SynthexBTC/Bitcoin-LoRa-Mesh/Solar-nRF52840-E22P868M30S/PCB/README.md

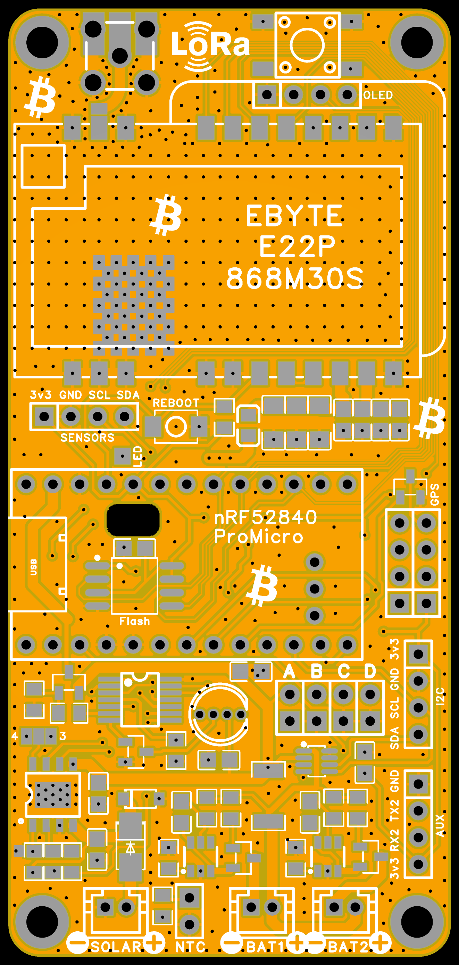
[picture p74: Solar-nRF52840-E22P868M30S/images/BitcoinMesh Solar nRF52840 E22P-868M30S - PCB Top.png]
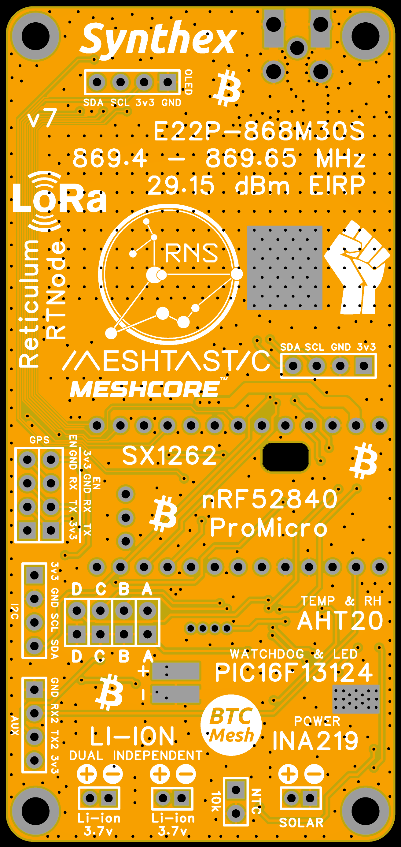
[picture p75: Solar-nRF52840-E22P868M30S/images/BitcoinMesh Solar nRF52840 E22P-868M30S - PCB Bottom.png]
&nbsp;&nbsp;
