SynthexBTC/Bitcoin-LoRa-Mesh/Module-nRF52840-E22P868M30S/PCB/README.md

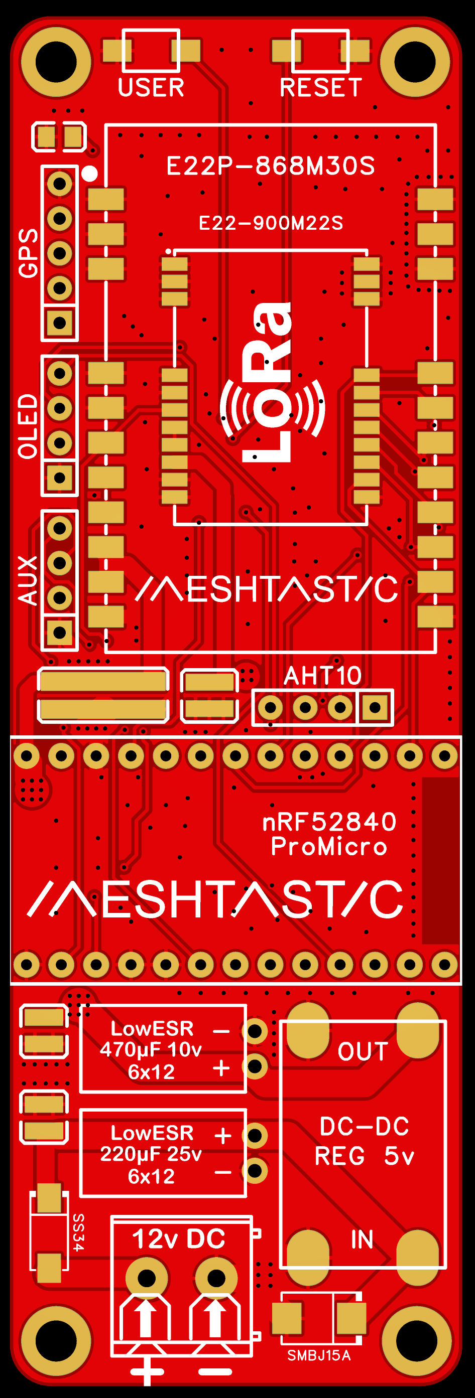
[picture p76: Module-nRF52840-E22P868M30S/images/BitcoinMesh HighPower Module nRF52840 - PCB Top.png]
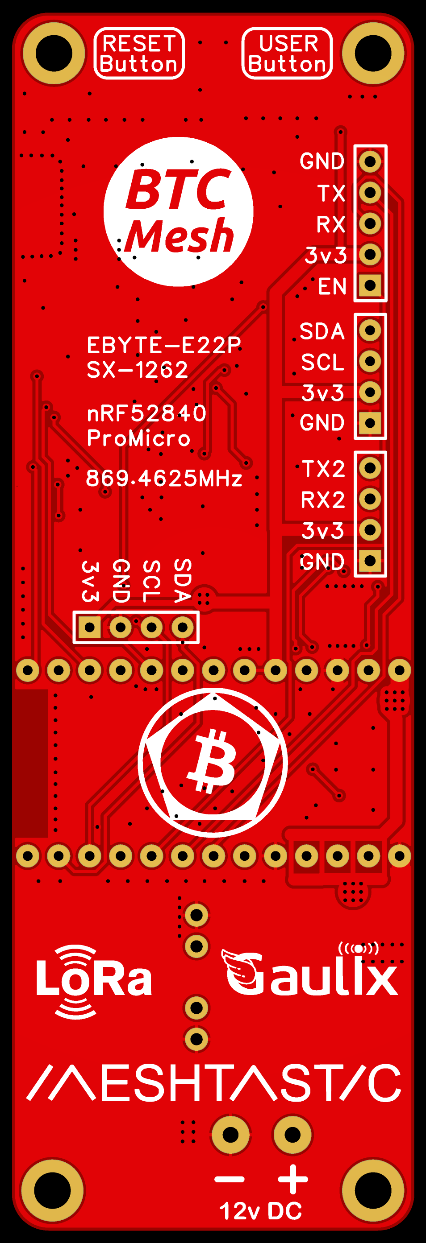
[picture p77: Module-nRF52840-E22P868M30S/images/BitcoinMesh HighPower Module nRF52840 - PCB Bottom.png]
&nbsp;&nbsp;
