SynthexBTC/Bitcoin-LoRa-Mesh/Module-nRF52840-HTRA62/PCB/README.md

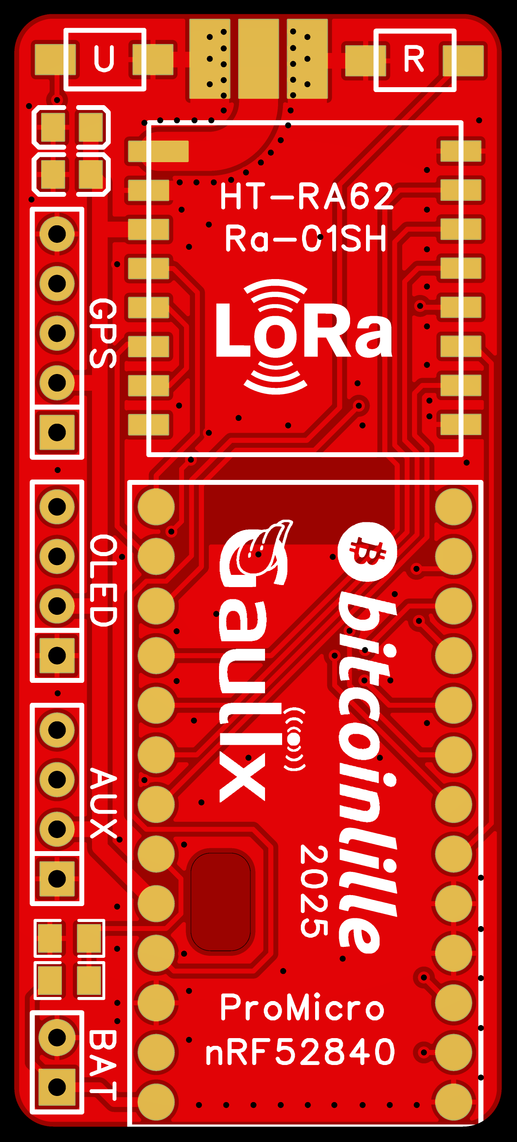
[picture p78: Module-nRF52840-HTRA62/images/BitcoinMesh Module nRF52840 - PCB Top.png]
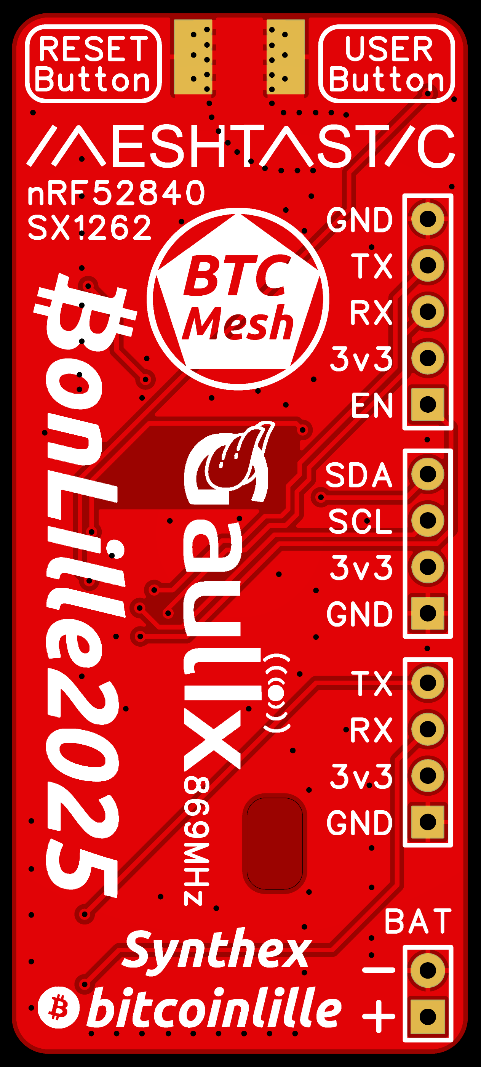
[picture p79: Module-nRF52840-HTRA62/images/BitcoinMesh Module nRF52840 - PCB Bottom.png]
&nbsp;&nbsp;
