SynthexBTC/Bitcoin-LoRa-Mesh/Shield-TDisplayS3-E22P868M30S/PCB/README.md

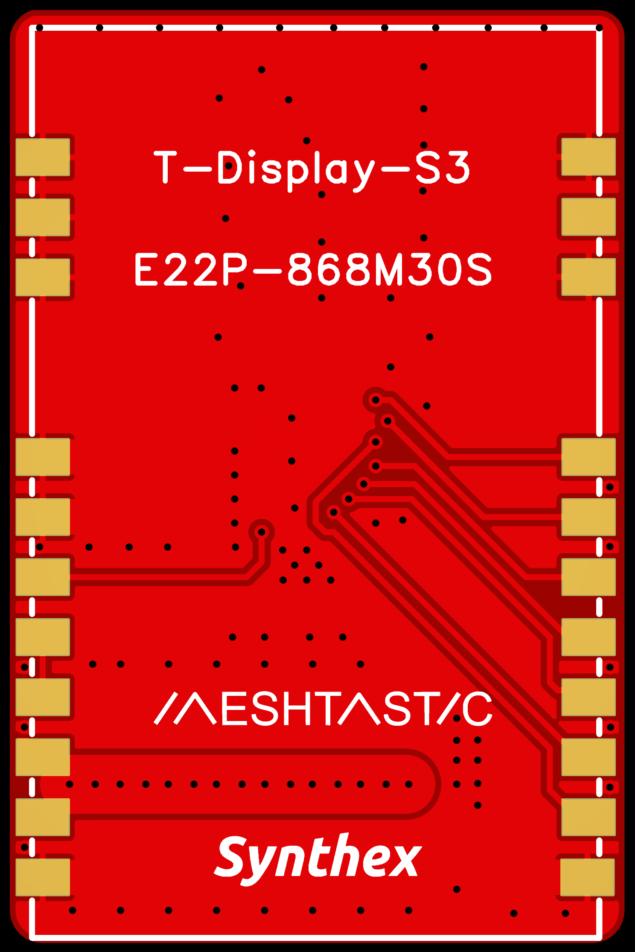
[picture p80: Shield-TDisplayS3-E22P868M30S/images/T-Display-S3 E22P-868M30S-IPX PCB Top.png]
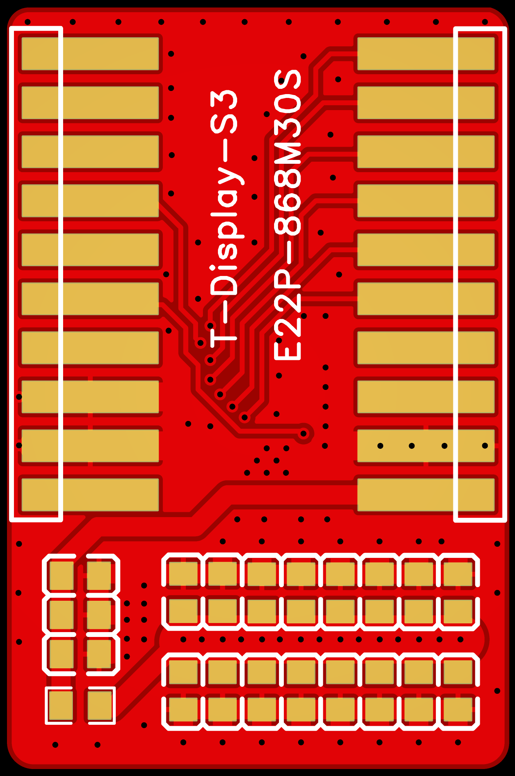
[picture p81: Shield-TDisplayS3-E22P868M30S/images/T-Display-S3 E22P-868M30S-IPX PCB Bottom.png]
&nbsp;&nbsp;

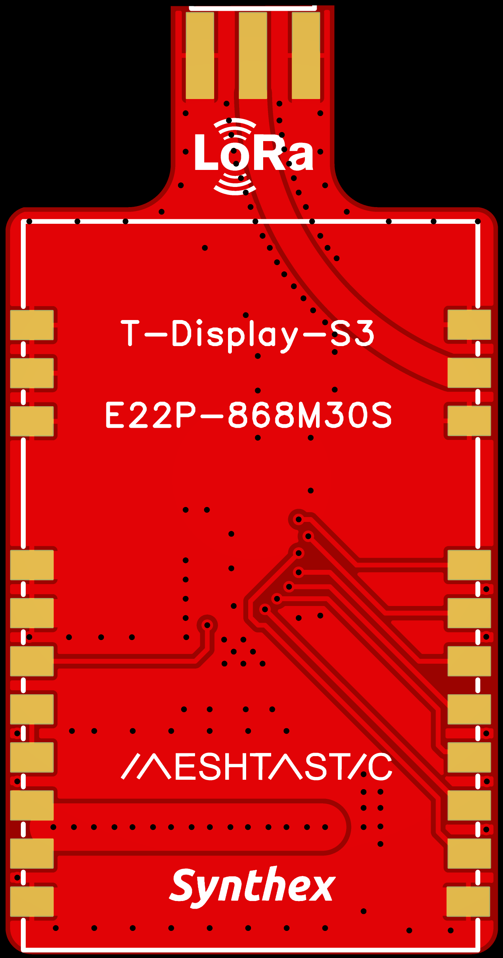
[picture p82: Shield-TDisplayS3-E22P868M30S/images/T-Display-S3 E22P-868M30S-SMA PCB Top.png]
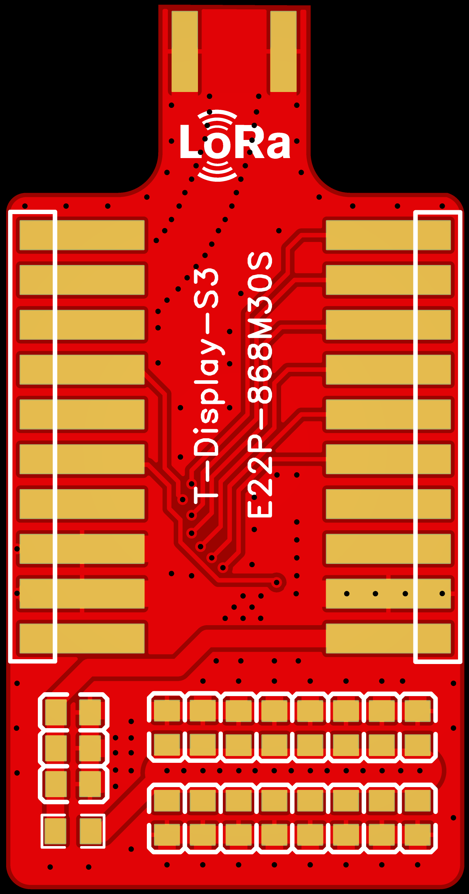
[picture p83: Shield-TDisplayS3-E22P868M30S/images/T-Display-S3 E22P-868M30S-SMA PCB Bottom.png]
&nbsp;&nbsp;
