SynthexBTC/Bitcoin-LoRa-Mesh/E22P-868M30S-Insider/images/E22P-868M30S - Comparison of the three.jpg

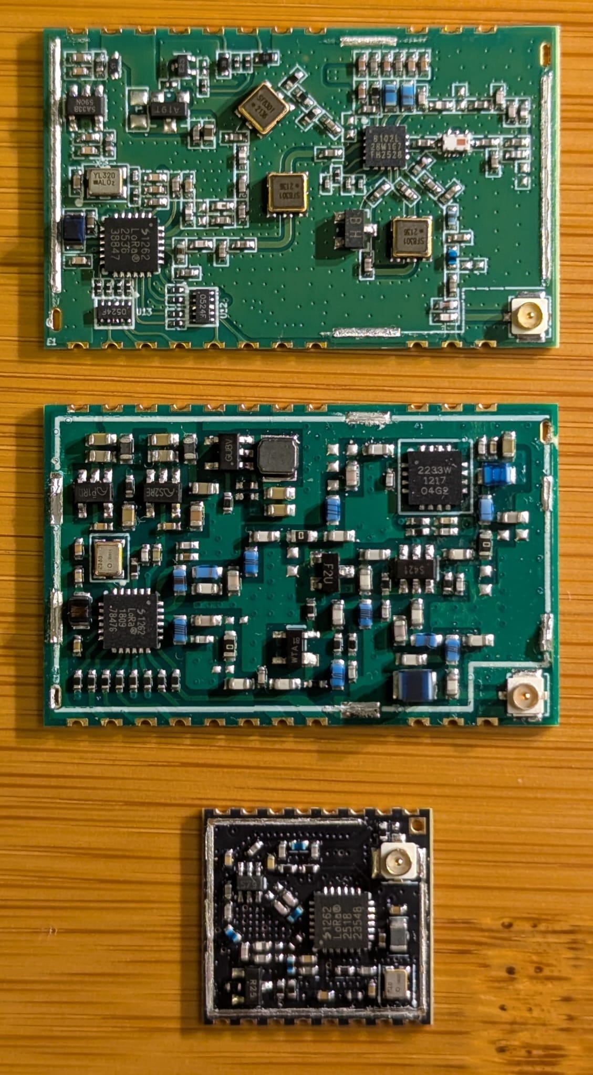
E22P-868M30S-Insider/images/E22P-868M30S - Comparison of the three.jpg
