SynthexBTC/Bitcoin-LoRa-Mesh/Mini-nRF52840-HTRA62/images/Mini-nRF52840-HTRA62 - 3D Up.png

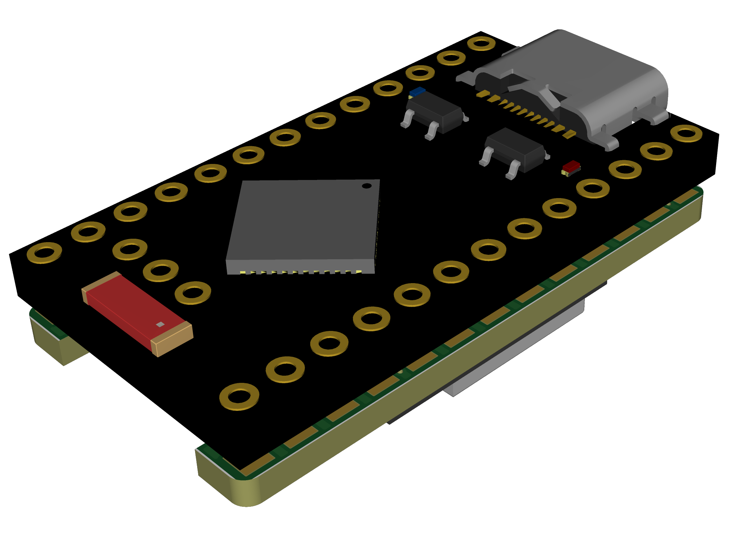
Mini-nRF52840-HTRA62/images/Mini-nRF52840-HTRA62 - 3D Up.png
