SynthexBTC/Bitcoin-LoRa-Mesh/Mini-nRF52840-HTRA62/images/Mini-nRF52840-HTRA62 - Orange Box 001.jpeg

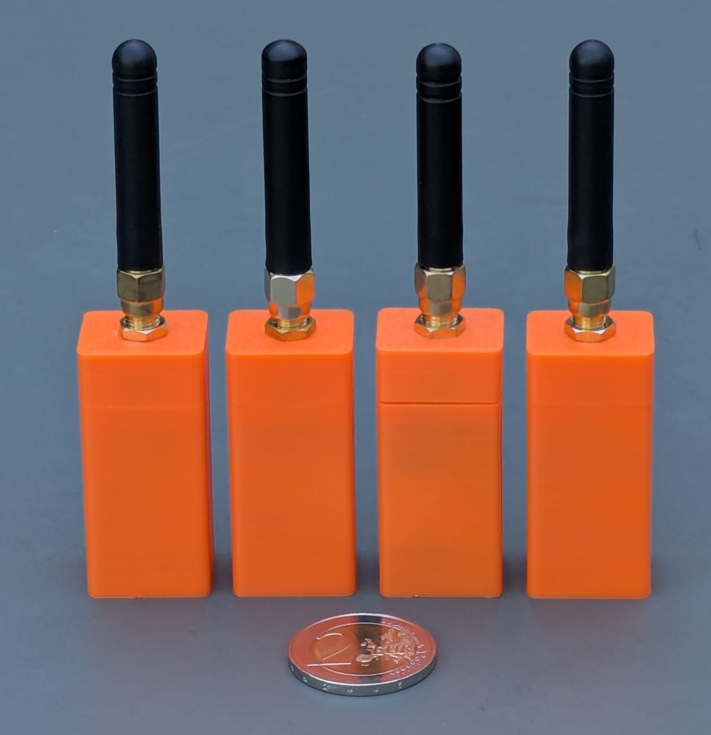
Mini-nRF52840-HTRA62/images/Mini-nRF52840-HTRA62 - Orange Box 001.jpeg
