SynthexBTC/Bitcoin-LoRa-Mesh/Module-nRF52840-HTRA62/images/Module nRF52840 HTRA62 - 18650 x9 002.jpeg

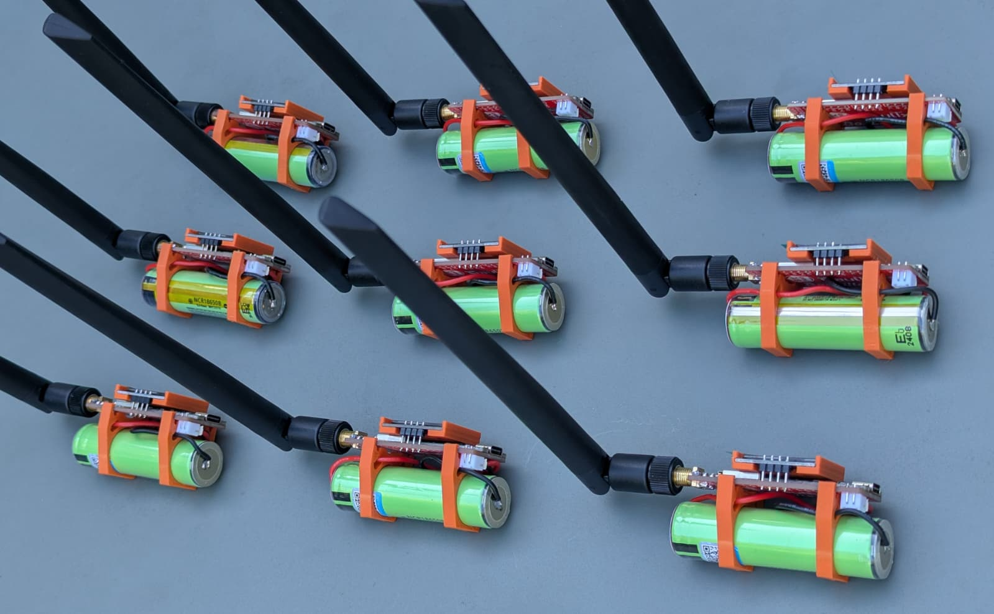
Module-nRF52840-HTRA62/images/Module nRF52840 HTRA62 - 18650 x9 002.jpeg
