SynthexBTC/Bitcoin-LoRa-Mesh/Solar-nRF52840-E22P868M30S/images/BitcoinMesh Solar nRF52840 E22P-868M30S - Final Open.jpeg

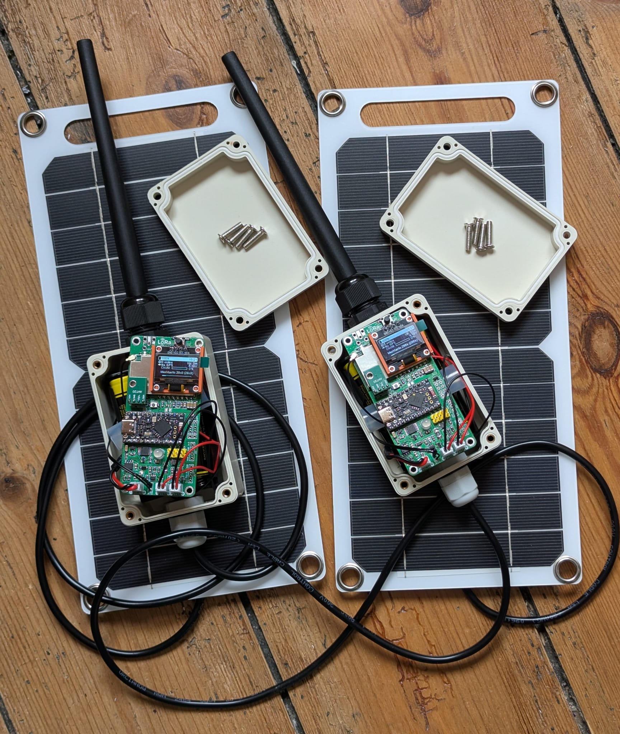
Solar-nRF52840-E22P868M30S/images/BitcoinMesh Solar nRF52840 E22P-868M30S - Final Open.jpeg
