SynthexBTC/Bitcoin-LoRa-Mesh/Wand-Solar-nRF52840-E22P868M30S/images/Wand Solar nRF52840 E22P-868M30S - 3D Holder.png

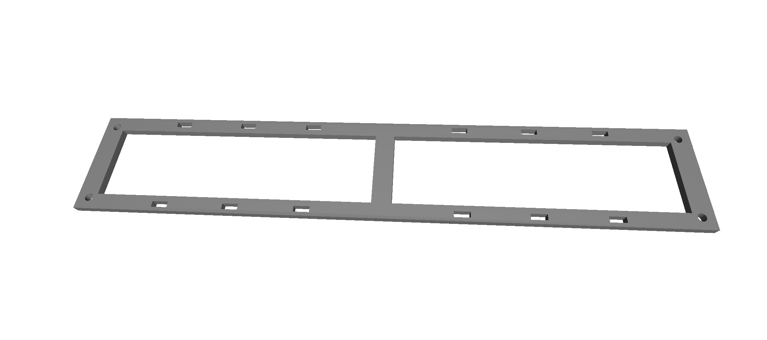
Wand-Solar-nRF52840-E22P868M30S/images/Wand Solar nRF52840 E22P-868M30S - 3D Holder.png
