SynthexBTC/Bitcoin-LoRa-Mesh/Wand-Solar-nRF52840-E22P868M30S/images/Wand Solar nRF52840 E22P-868M30S - Batteries Holder.jpeg

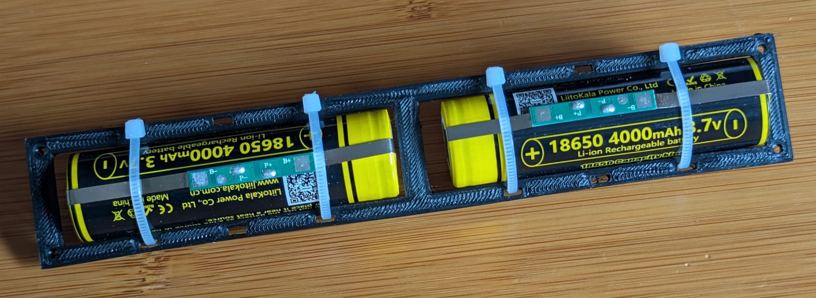
Wand-Solar-nRF52840-E22P868M30S/images/Wand Solar nRF52840 E22P-868M30S - Batteries Holder.jpeg
